antonjan/IQ_Modulator/doc/Block_Diagram_SDR_Software_configuration.png

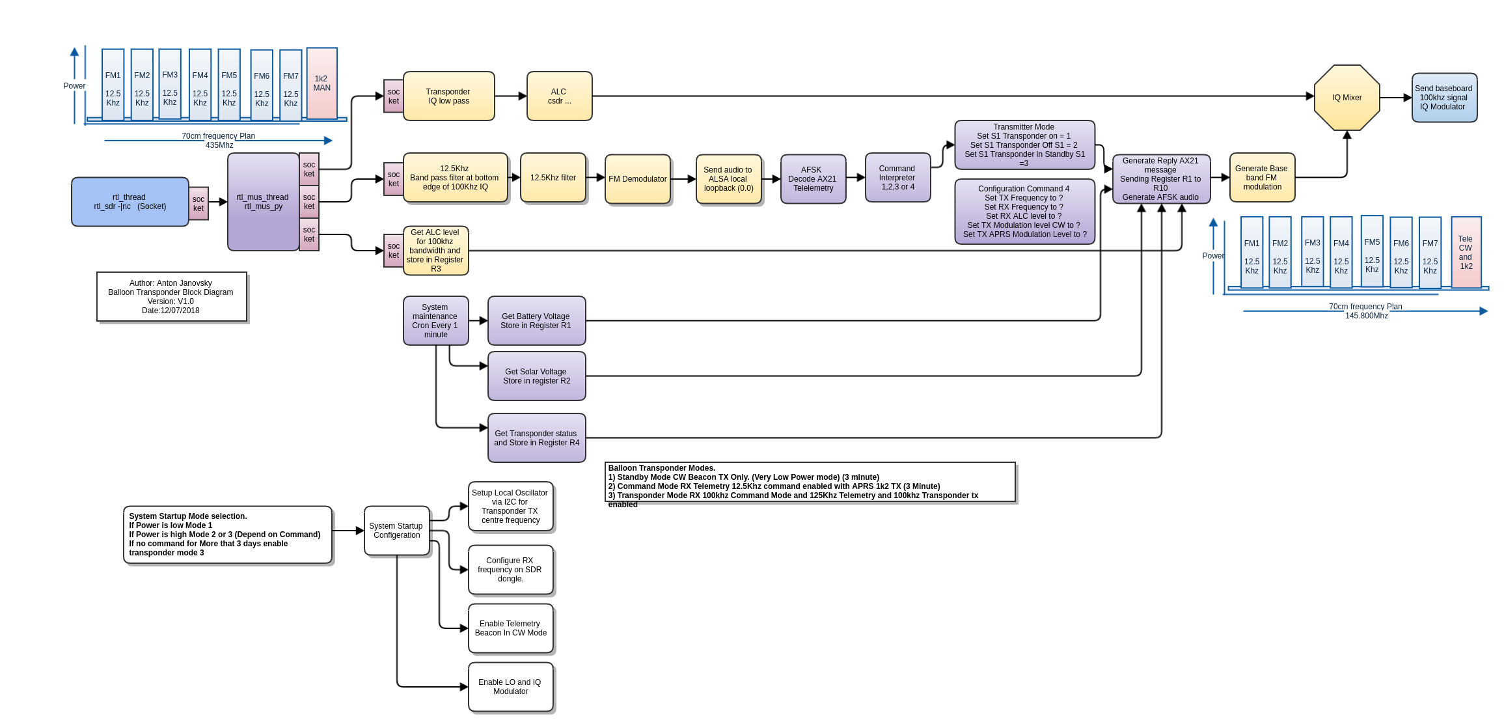
doc/Block_Diagram_SDR_Software_configuration.png
