antonjan/IQ_Modulator/doc/Transponder_Signal_Path.jpg

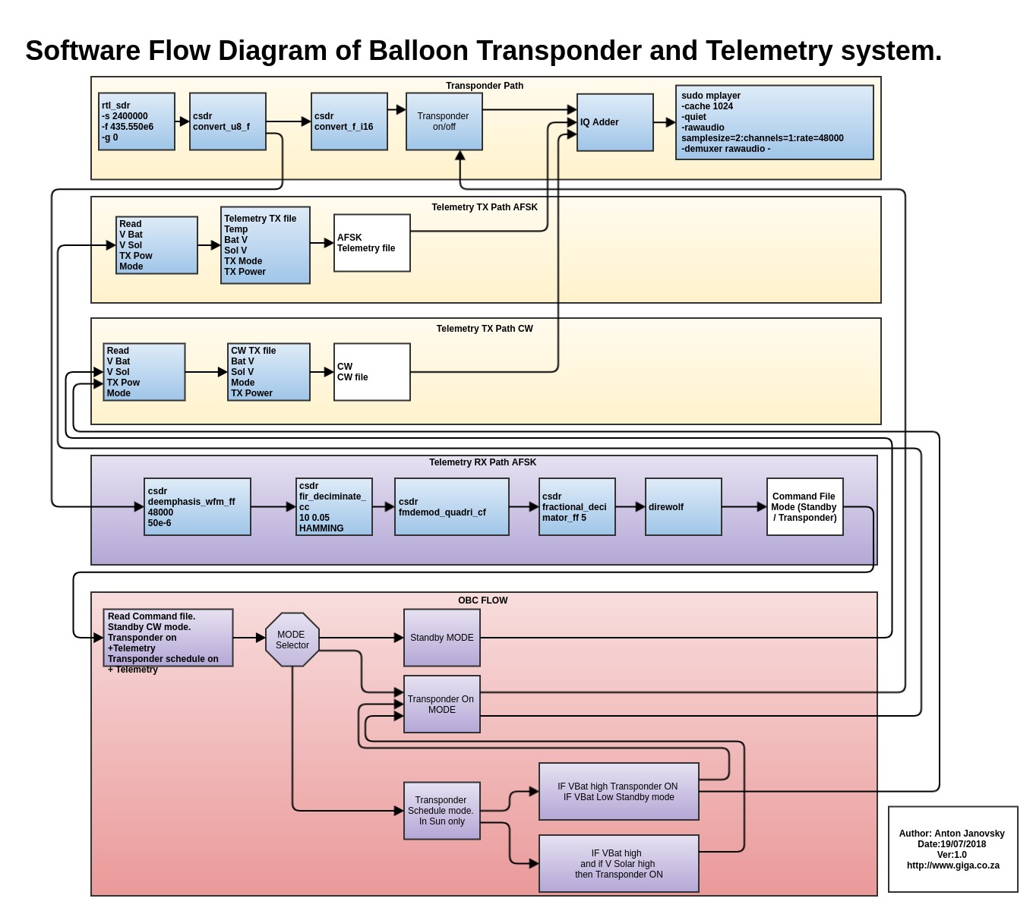
doc/Transponder_Signal_Path.jpg
