antonjan/IQ_Modulator/IQ_Modulator_/vhf_uhf_IQ_Modulator_V2-F.CrtYd.pdf

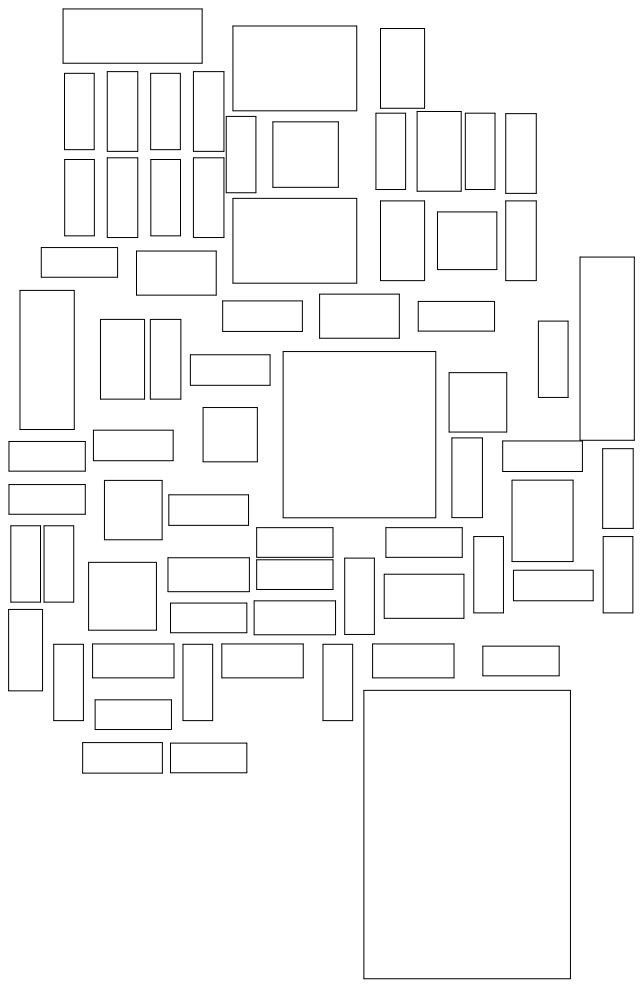
[picture p14: page 1]
