antonjan/IQ_Modulator/IQ_Modulator_/vhf_uhf_IQ_Modulator_V2-F.Cu.pdf

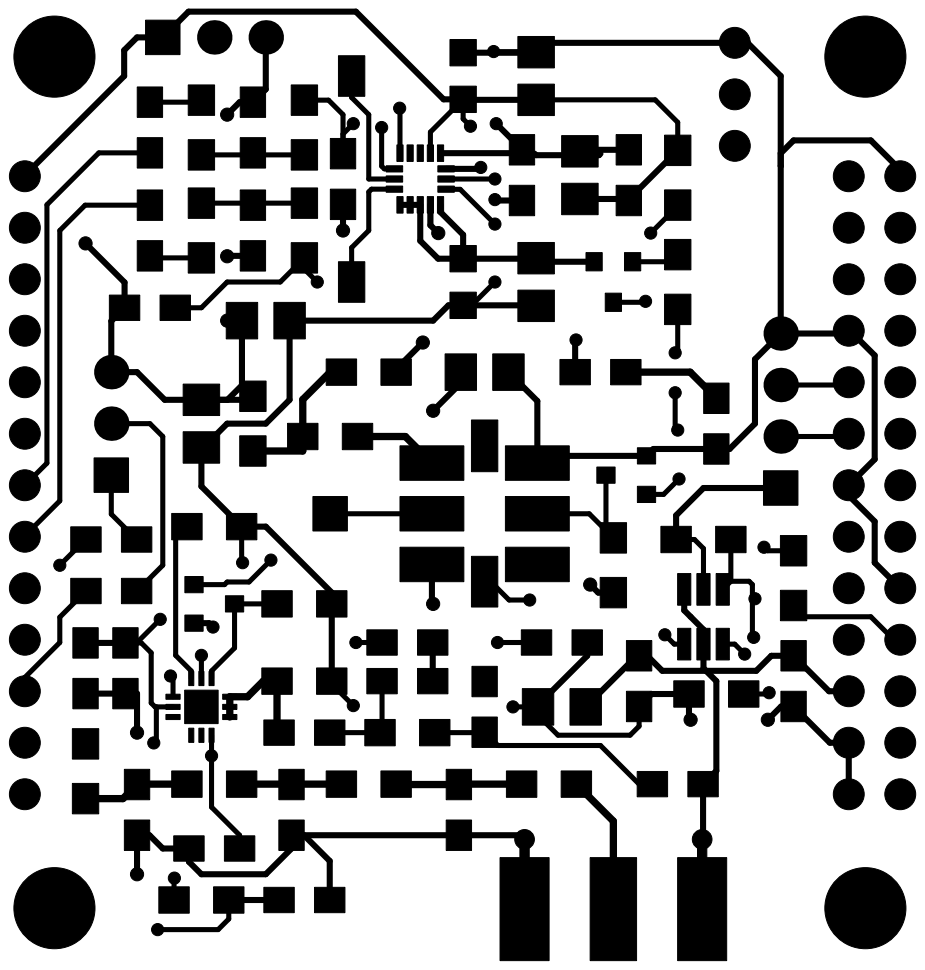
[picture p15: page 1]
