antonjan/IQ_Modulator/IQ_Modulator_/vhf_uhf_IQ_Modulator_V2-F.Fab.pdf

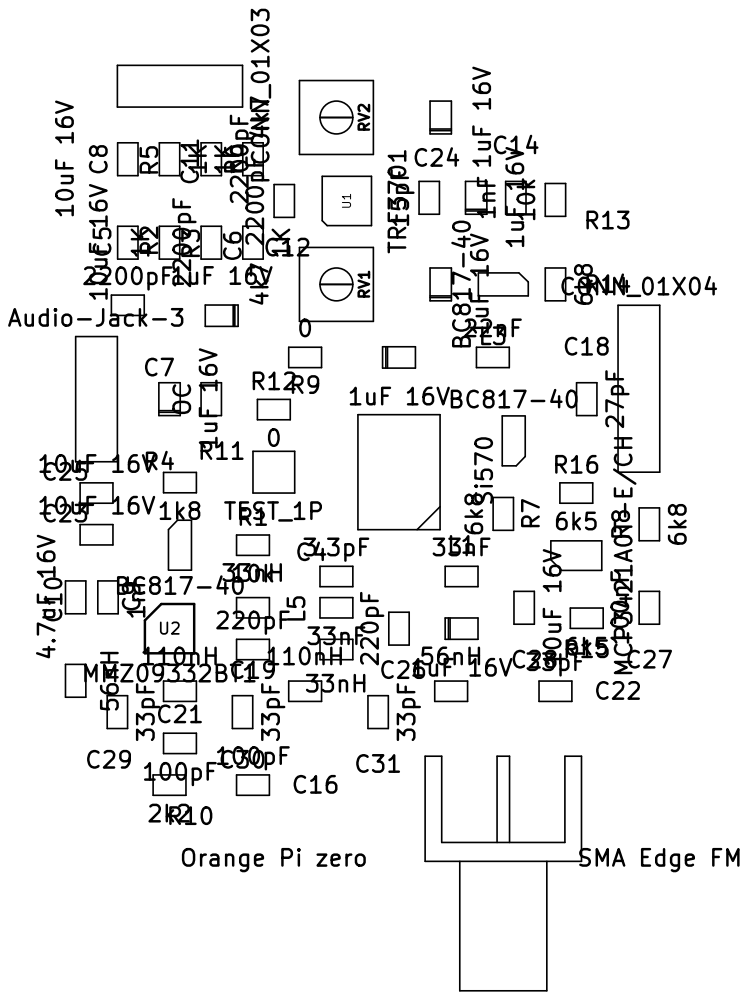
[picture p16: page 1]
