antonjan/IQ_Modulator/IQ_Modulator_/vhf_uhf_IQ_Modulator_V2-F.Mask.pdf

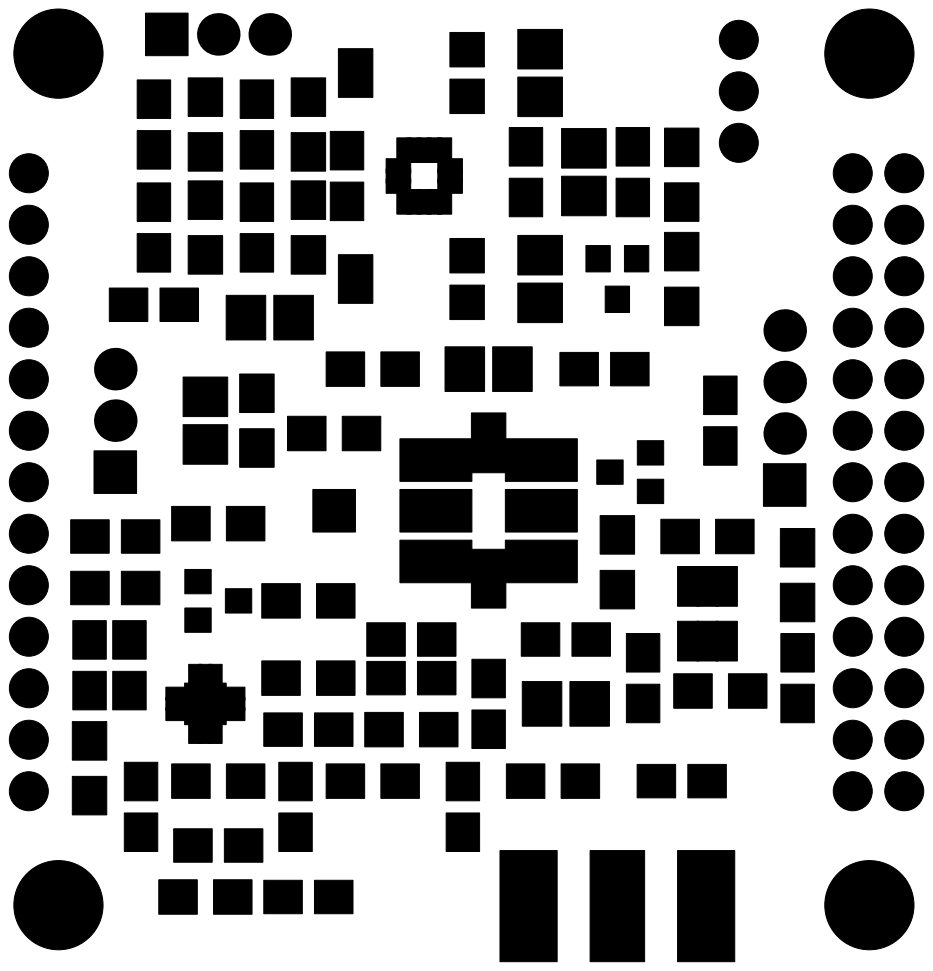
[picture p17: page 1]
