antonjan/IQ_Modulator/IQ_Modulator_/vhf_uhf_IQ_Modulator_V2-F.Paste.pdf

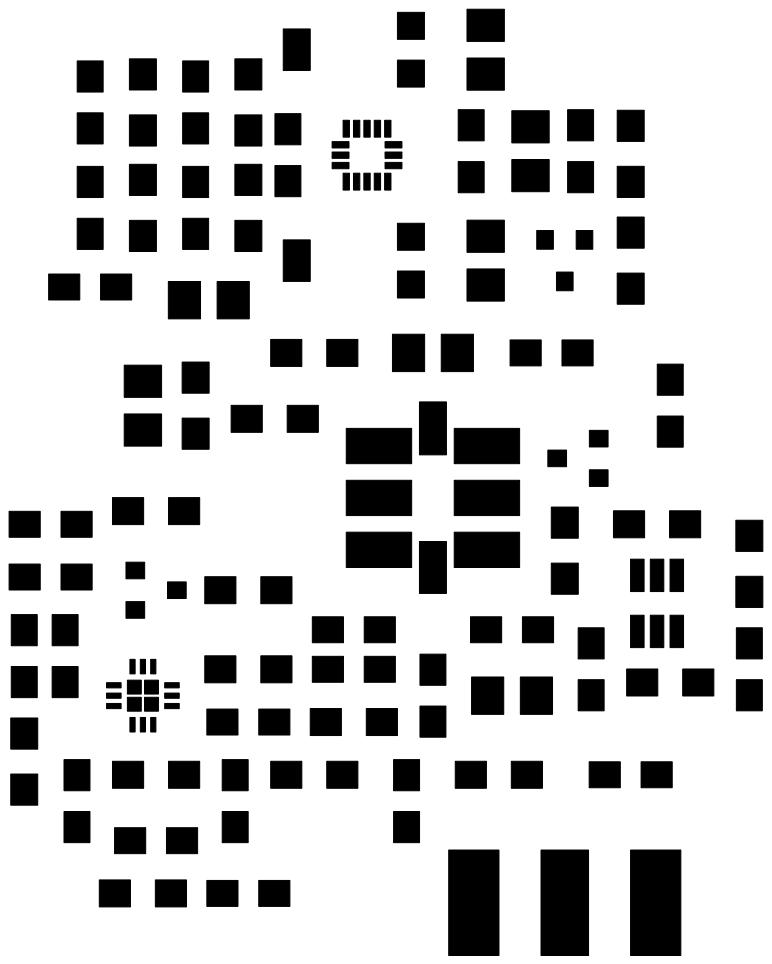
[picture p18: page 1]
