antonjan/IQ_Modulator/IQ_Modulator_/vhf_uhf_IQ_Modulator_V2-F.SilkS.pdf

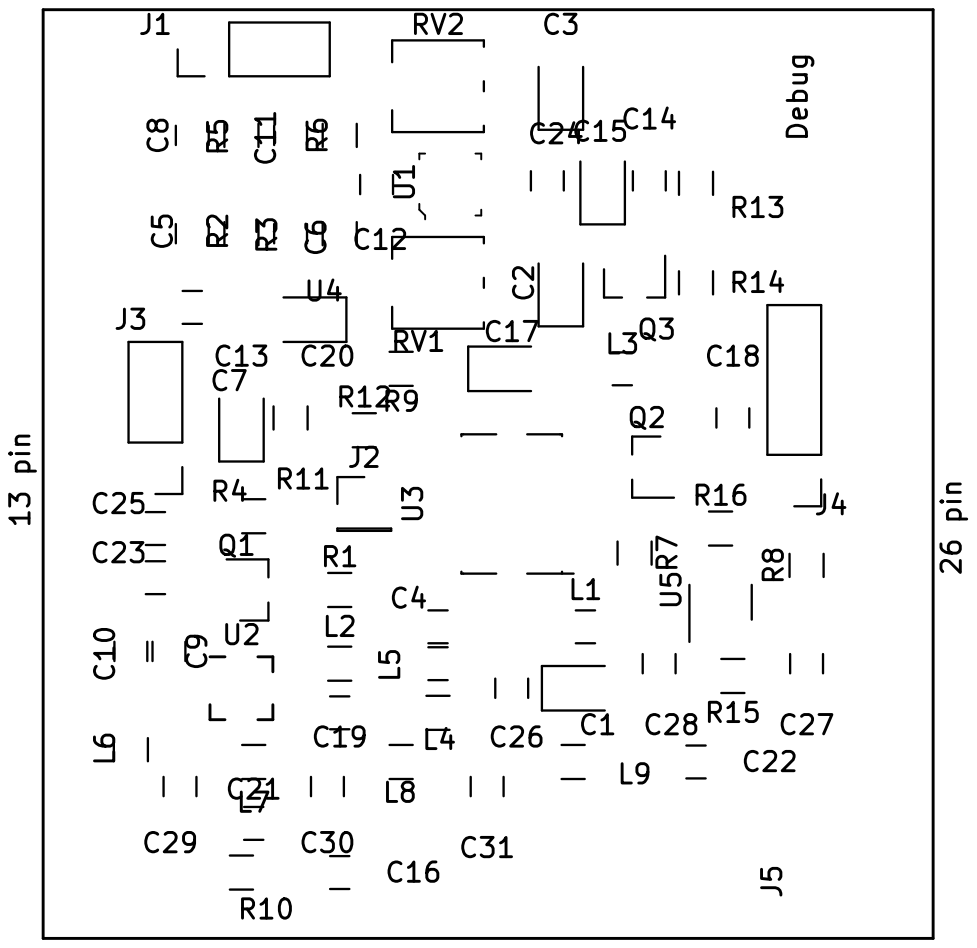
[picture p19: page 1]
