antonjan/IQ_Modulator/doc/IQ_modulator_V2.pdf

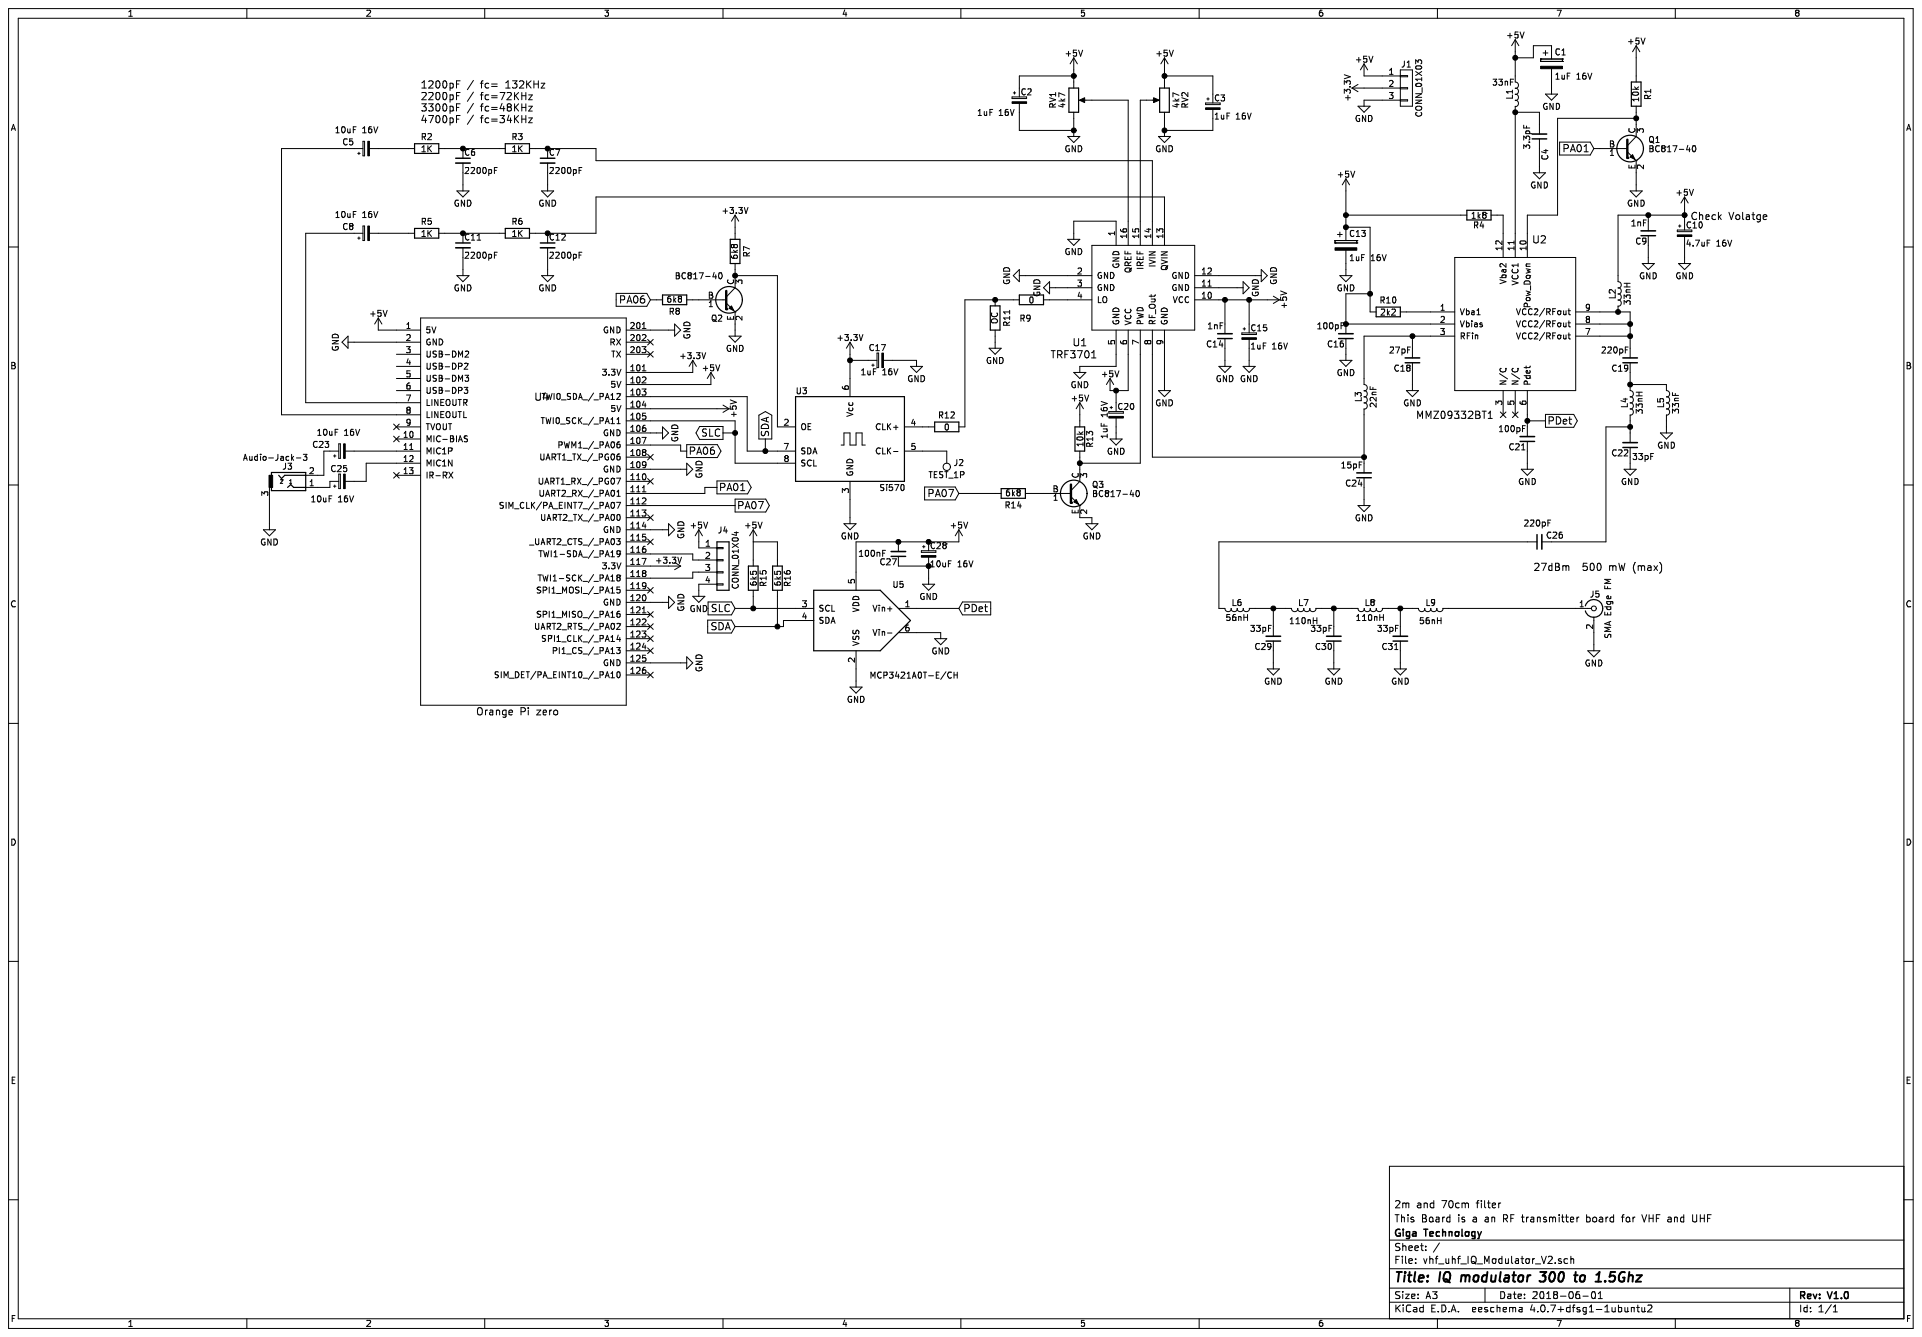
[picture p20: page 1]
