antonjan/IQ_Modulator/doc/IQ_modulator_V1.pdf

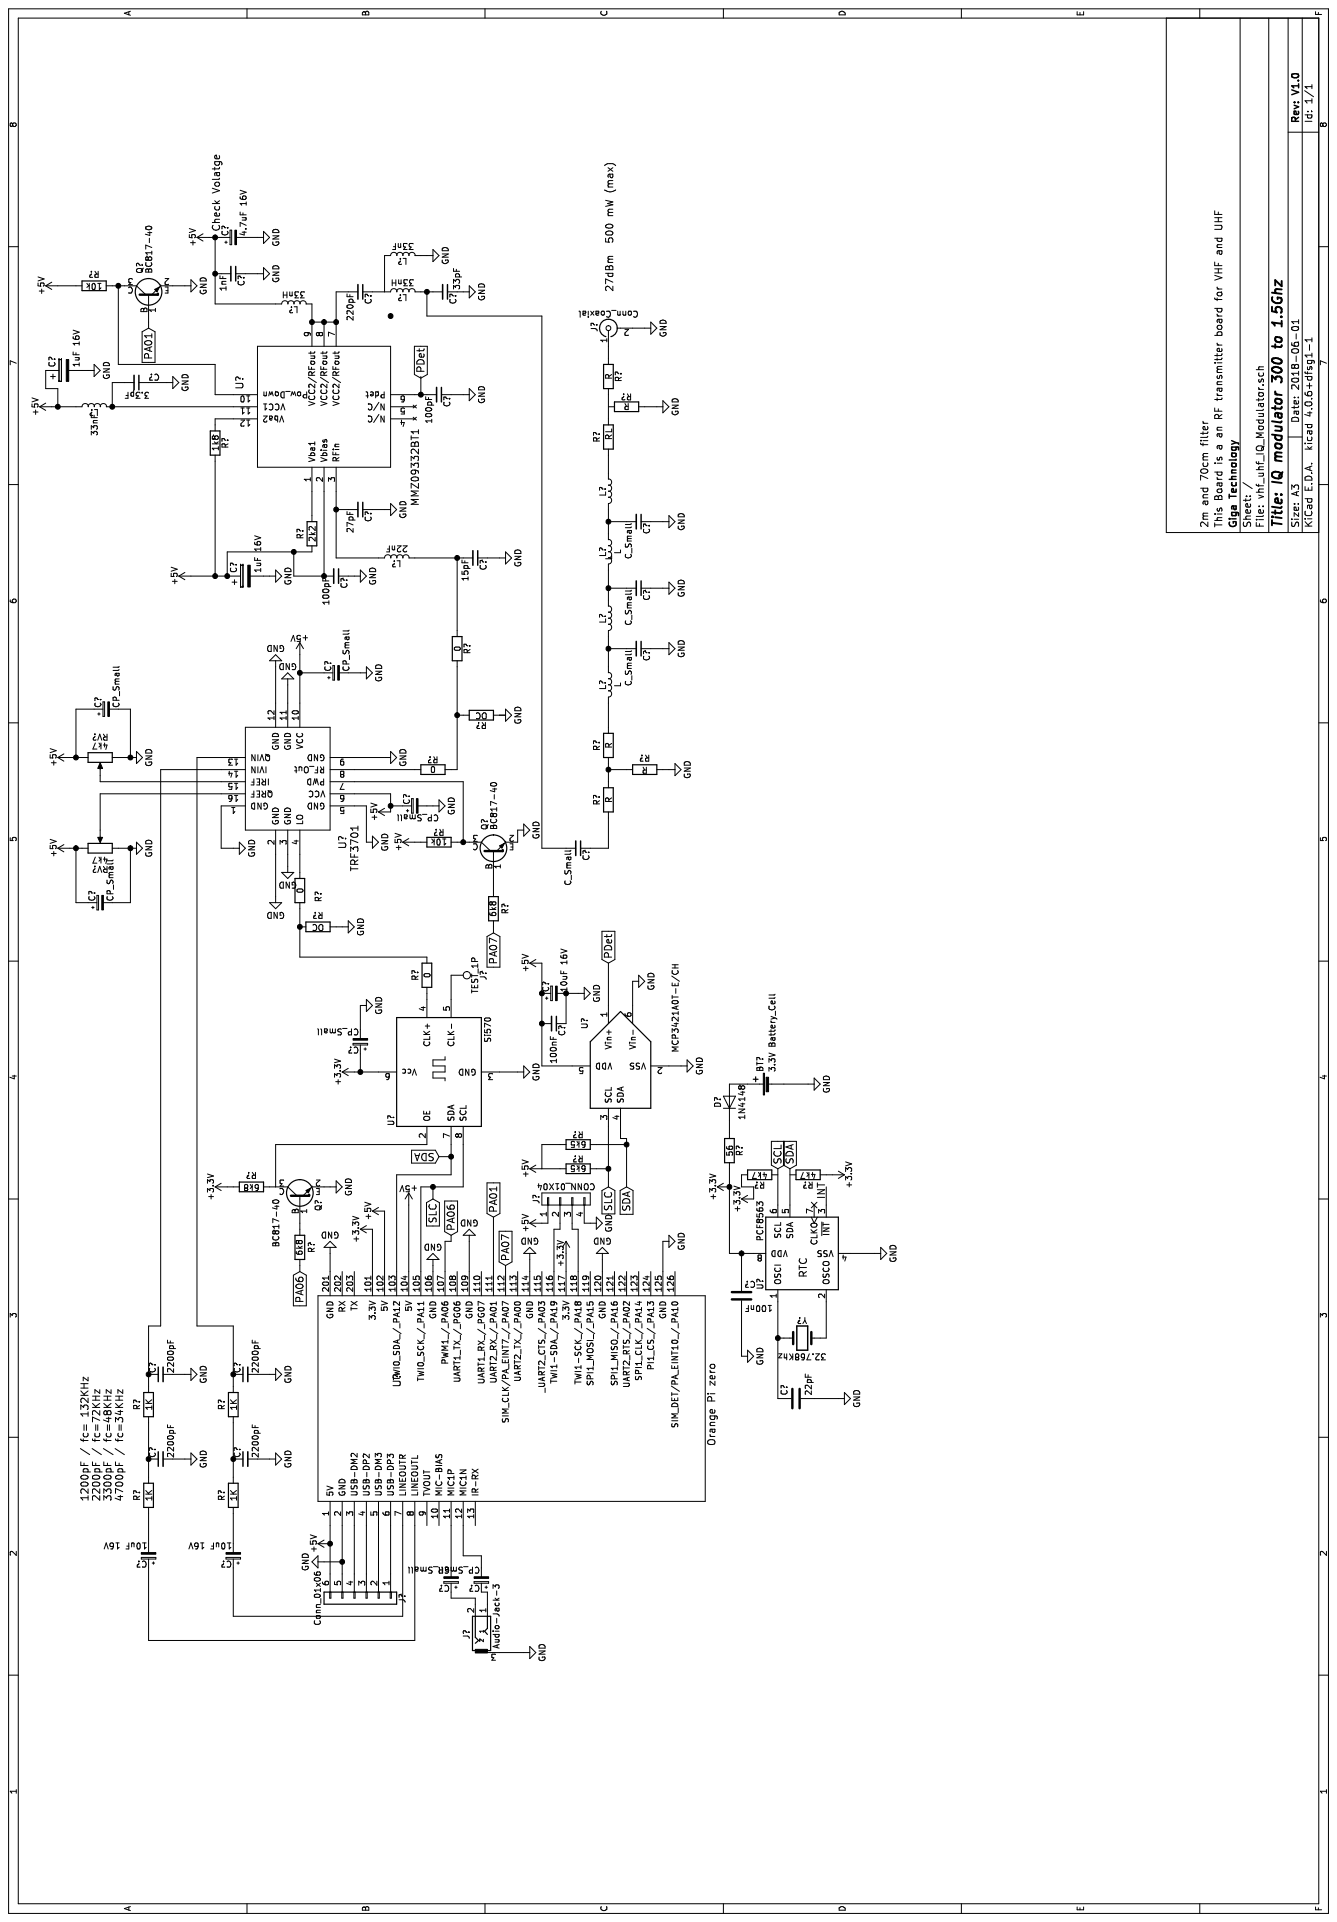
[picture p21: page 1]
