antonjan/IQ_Modulator/psk/varicode.c

#include <stdio.h>
#include <stdlib.h>


// each character is separated by two zeros. The bits are sent msbit first.
static const int varicode_table[] = {
  0xAAC0, // ASCII =   0	1010101011
  0xB6C0, // ASCII =   1	1011011011
  0xBB40, // ASCII =   2	1011101101
  0xDDC0, // ASCII =   3	1101110111
  0xBAC0, // ASCII =   4	1011101011
  0xD7C0, // ASCII =   5	1101011111
  0xBBC0, // ASCII =   6	1011101111
  0xBF40, // ASCII =   7	1011111101
  0xBFC0, // ASCII =   8	1011111111
  0xEF00, // ASCII =   9	11101111
  0xE800, // ASCII =  10	11101
  0xDBC0, // ASCII =  11	1101101111
  0xB740, // ASCII =  12	1011011101
  0xF800, // ASCII =  13	11111
  0xDD40, // ASCII =  14	1101110101
  0xEAC0, // ASCII =  15	1110101011
  0xBDC0, // ASCII =  16	1011110111
  0xBD40, // ASCII =  17	1011110101
  0xEB40, // ASCII =  18	1110101101
  0xEBC0, // ASCII =  19	1110101111
  0xD6C0, // ASCII =  20	1101011011
  0xDAC0, // ASCII =  21	1101101011
  0xDB40, // ASCII =  22	1101101101
  0xD5C0, // ASCII =  23	1101010111
  0xDEC0, // ASCII =  24	1101111011
  0xDF40, // ASCII =  25	1101111101
  0xEDC0, // ASCII =  26	1110110111
  0xD540, // ASCII =  27	1101010101
  0xD740, // ASCII =  28	1101011101
  0xEEC0, // ASCII =  29	1110111011
  0xBEC0, // ASCII =  30	1011111011
  0xDFC0, // ASCII =  31	1101111111
  0x8000, // ASCII = ' '	1
  0xFF80, // ASCII = '!'	111111111
  0xAF80, // ASCII = '"'	101011111
  0xFA80, // ASCII = '#'	111110101
  0xED80, // ASCII = '$'	111011011
  0xB540, // ASCII = '%'	1011010101
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
  0xAD50, // ASCII = 240	101011010101
  0xAD70, // ASCII = 241	101011010111
  0xADB0, // ASCII = 242	101011011011
  0xADD0, // ASCII = 243	101011011101
  0xADF0, // ASCII = 244	101011011111
  0xAEB0, // ASCII = 245	101011101011
  0xAED0, // ASCII = 246	101011101101
  0xAEF0, // ASCII = 247	101011101111
  0xAF50, // ASCII = 248	101011110101
  0xAF70, // ASCII = 249	101011110111
  0xAFB0, // ASCII = 250	101011111011
  0xAFD0, // ASCII = 251	101011111101
  0xAFF0, // ASCII = 252	101011111111
  0xB550, // ASCII = 253	101101010101
  0xB570, // ASCII = 254	101101010111
  0xB5B0 // ASCII = 255	101101011011
};

int main(int argc, char *argv[]) {
	int i, m, l, len;

	for (i = 0; i < sizeof(varicode_table) / sizeof(varicode_table[0]); i++) {
		l = 0;
		len = 0;
		m = varicode_table[i];
		while ((m & 1) == 0)
			m >>= 1;
		for (; m; m >>= 1) {
			l <<= 1;
			if ((m & 1) != 0)
				l++;
			len++;
		}
		len += 2;
		printf("\t{%2d, 0x%04x}, /* ASCII = ", len, l);
		if (i < 32 || i > 126)
			printf("%3d ", i);
		else
			printf("'%c' ", i);
		for (m = l; len; m >>= 1, len--)
			printf("%c", '0' + (m & 1));
		printf(" */\n");
	}
	return 0;
}
